kamocat/rf_gen/rf_gen.asc

C3: cap; 220p
C4: cap; 270p
C5: cap; 1.5n
C7: cap; 100n
C9: cap; 39p
C10: cap; 39p
C11: cap; 232p
Cds2: cap; 110p
Cds: cap; 10p
Cgd: cap; .8p
Cgs: cap; 330p
D1: diode
D2: diode
L1: ind; 220n; Rser=11m
L2: ind; 650n; Rser=45m
L3: ind; 90n; Rser=5.5m
L4: ind; 110n; Rser=6.5m
L5: ind; 880n; Rser=50m
L6: ind; 3.5µ; Rser=100m
L7: ind; 594n; Rser=40m
R1: res; 50
R2: res; 1k
S1: sw
S2: sw
V1: voltage; 12
V2: voltage; SINE(2.5 3 13.56Meg)
V3: voltage; 150
Named nets: 0
.model MYSW SW(Ron=0.01, Roff=1Meg, Vt=2.7, Vh=-.4)
.tran 0 5u 0 1n
