kamocat/rf_gen/LTSpice/filter.asc

C1: cap; 270p; Rser=3
C2: cap; 180p; Rser=3
L1: ind; 500n; Rser=.75
L2: ind; 766n; Rser=.75
R1: res; 30
V1: voltage; ""; AC 1 0
Named nets: 0
.ac oct 10k 1Meg 100Meg
