kamocat/rf_gen/LTSpice/rf_gen.asc

C1: cap; 331p
C3: cap; 220p
C4: cap; 270p
C5: cap; 1.22n
C7: cap; 100n
C9: cap; 180p
C10: cap; 180p
C11: cap; 270p
D1: diode
D2: diode
L1: ind; 220n; Rser=11m
L2: ind; 500n; Rser=45m
L3: ind; 90n; Rser=5.5m
L4: ind; 110n; Rser=6.5m
L5: ind; 880n; Rser=50m
L6: ind; 766n; Rser=100m
L7: ind; 500n; Rser=40m
L8: ind; 10p; Rser=.1
R1: res; 20
R2: res; 1k
R3: res; 1
R4: res; 1Meg
S1: sw
U2: GaN_LTspice_GS61004B_L3V4P2
V1: voltage; 12
V2: voltage; PULSE(0 5 0 10n 10n 27n 73.7n)
V3: voltage; 150
Named nets: 0
.tran 0 3u 2u 1n
.lib GaN_LTspice_GS61004B_L3V4P2.lib
.lib G3R30MT12J.lib
.model MYSW SW(Ron=10m, Roff=1Meg, Vt=5, Vh=-4)
